OLIMEX/STMP157-BASE-SOM-EVB/HARDWARE/STMP157-BASE-SOM-EVB-Rev.B/3d/SOT-23.step

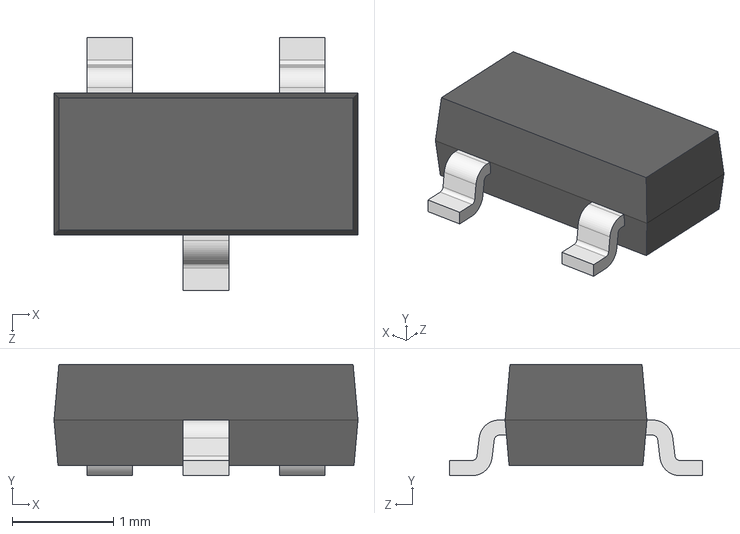
[picture p16: CAD file, 2023-11-24]
HARDWARE/STMP157-BASE-SOM-EVB-Rev.B/3d/SOT-23.step
3.00 x 1.10 x 2.50 mm
