OLIMEX/STMP157-BASE-SOM-EVB/HARDWARE/STMP157-BASE-SOM-EVB-Rev.B/3d/HN1x3-PinHeader_1x03_P2.54mm_Vertical.step

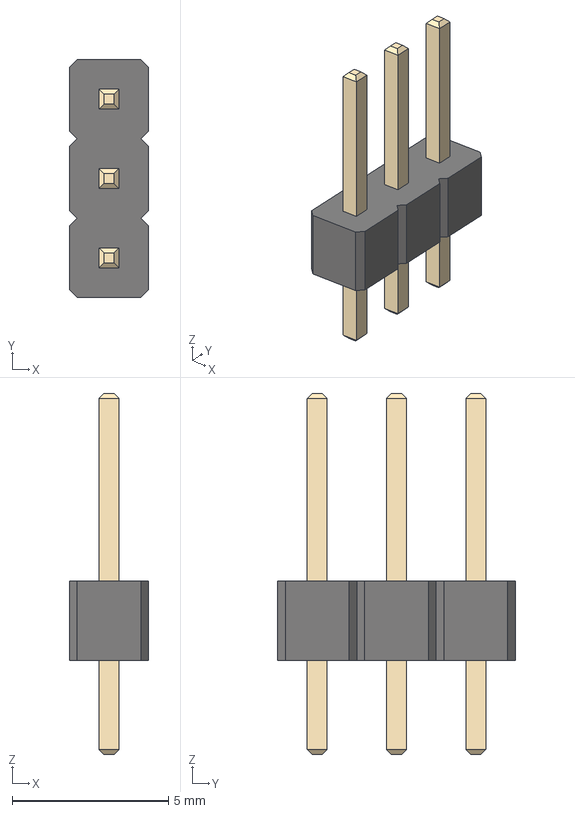
[picture p17: CAD file, 2023-11-24]
HARDWARE/STMP157-BASE-SOM-EVB-Rev.B/3d/HN1x3-PinHeader_1x03_P2.54mm_Vertical.step
2.54 x 7.62 x 11.5 mm
