OLIMEX/STMP157-BASE-SOM-EVB/HARDWARE/STMP157-BASE-SOM-EVB-Rev.B/3d/dshp04ts-s.stp

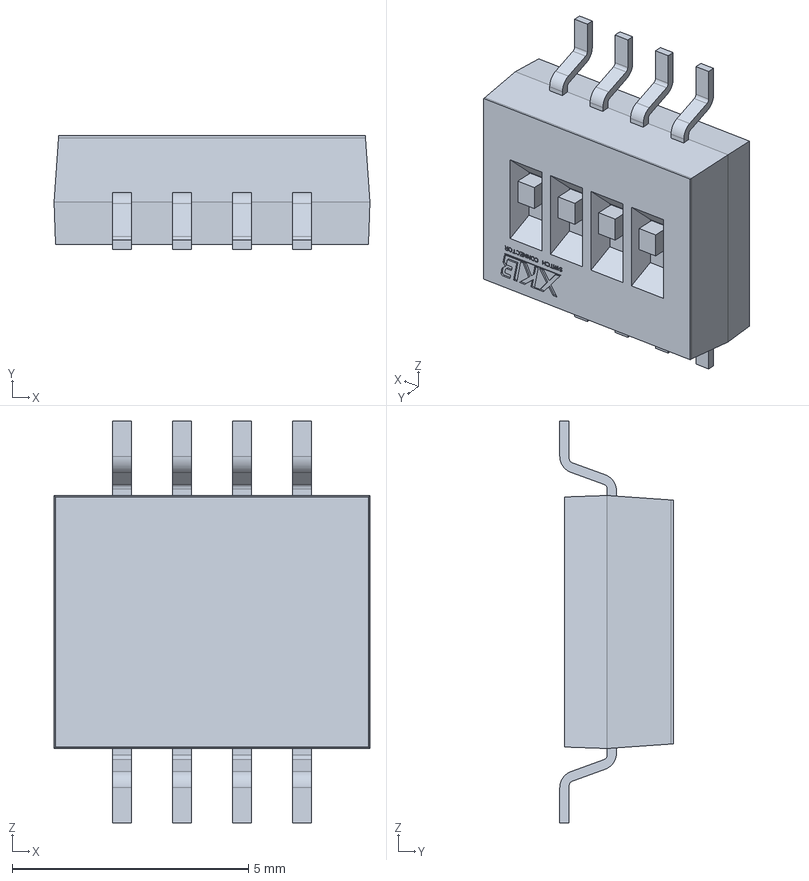
[picture p18: CAD file, 2023-11-24]
HARDWARE/STMP157-BASE-SOM-EVB-Rev.B/3d/dshp04ts-s.stp
6.68 x 2.40 x 8.50 mm
