OLIMEX/STMP157-BASE-SOM-EVB/HARDWARE/STMP157-BASE-SOM-EVB-Rev.B/3d/QFN48-0.5.STEP

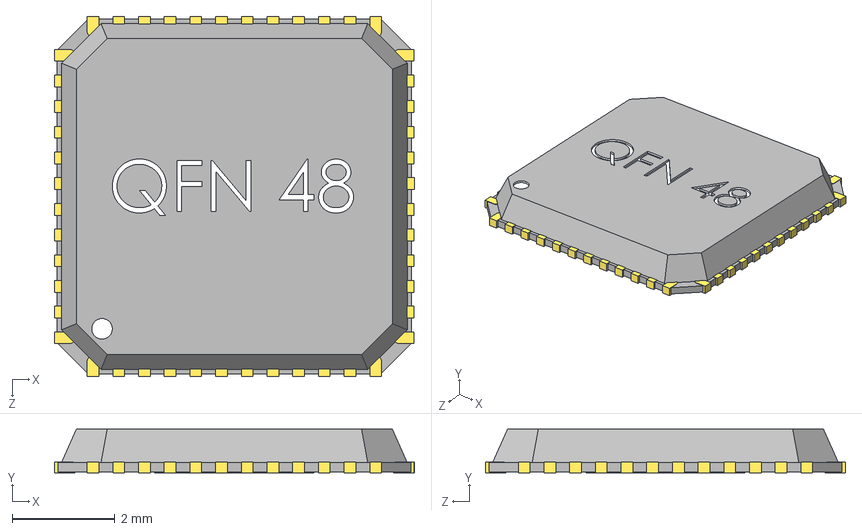
[picture p19: CAD file, 2023-11-24]
HARDWARE/STMP157-BASE-SOM-EVB-Rev.B/3d/QFN48-0.5.STEP
7.00 x 0.85 x 7.01 mm
User Library-QFN48-1_Body
User Library-QFN48-1_Pins
