OLIMEX/STMP157-BASE-SOM-EVB/HARDWARE/STMP157-BASE-SOM-EVB-Rev.B/3d/Audio_Jack-3.5mm---CUI_SJ1-3515-SMT-TR.step

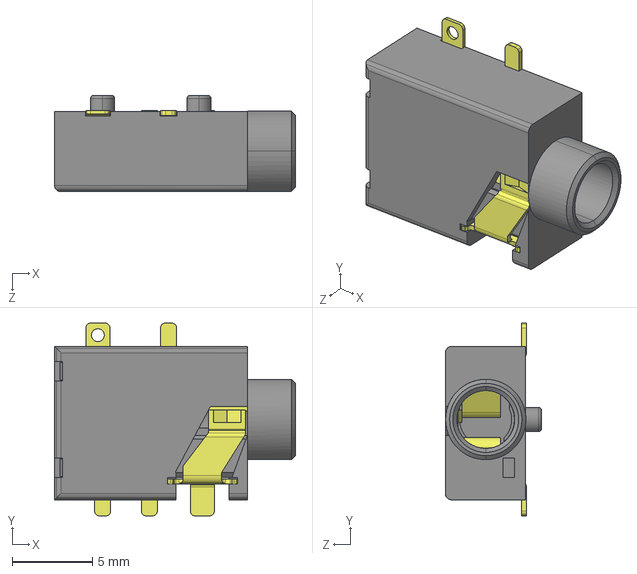
[picture p20: CAD file, 2023-11-24]
HARDWARE/STMP157-BASE-SOM-EVB-Rev.B/3d/Audio_Jack-3.5mm---CUI_SJ1-3515-SMT-TR.step
15.0 x 12.0 x 6.00 mm
