OLIMEX/STMP157-BASE-SOM-EVB/HARDWARE/STMP157-BASE-SOM-EVB-Rev.B/3d/GBH254SMT-40(B-V-40-LF).stp

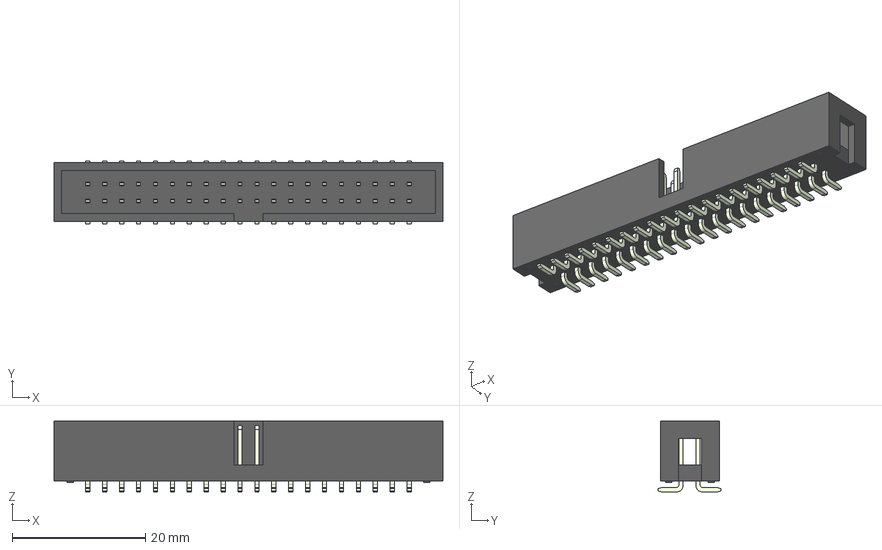
[picture p22: CAD file, 2023-11-24]
HARDWARE/STMP157-BASE-SOM-EVB-Rev.B/3d/GBH254SMT-40(B-V-40-LF).stp
58.4 x 9.50 x 10.6 mm
