OLIMEX/STMP157-BASE-SOM-EVB/HARDWARE/STMP157-BASE-SOM-EVB-Rev.B/3d/JST_B2B-PH-SM4-TB(DW02R).step

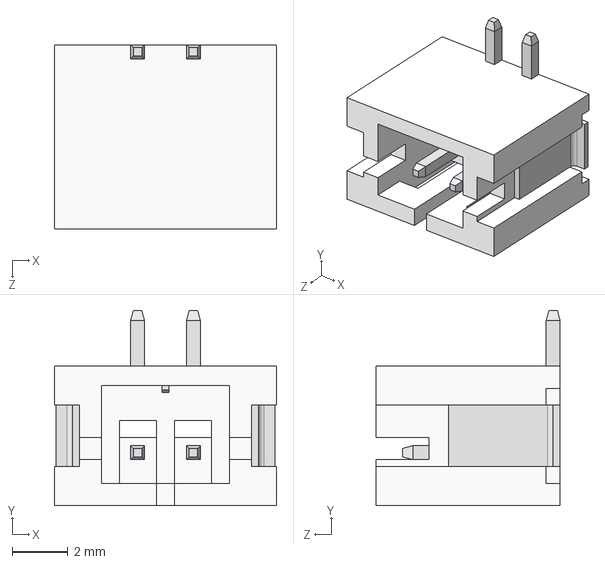
[picture p23: CAD file, 2023-11-24]
HARDWARE/STMP157-BASE-SOM-EVB-Rev.B/3d/JST_B2B-PH-SM4-TB(DW02R).step
7.95 x 7.00 x 6.60 mm
