OLIMEX/STMP157-BASE-SOM-EVB/HARDWARE/STMP157-BASE-SOM-EVB-Rev.B/3d/DF12(3.0)-40DS-0.5V.stp

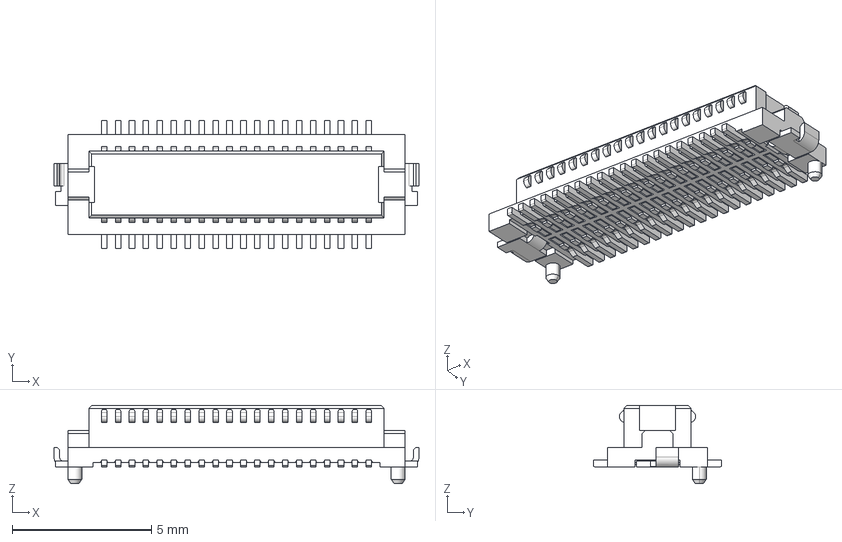
[picture p24: CAD file, 2023-11-24]
HARDWARE/STMP157-BASE-SOM-EVB-Rev.B/3d/DF12(3.0)-40DS-0.5V.stp
13.1 x 4.60 x 2.80 mm
