OLIMEX/STMP157-BASE-SOM-EVB/HARDWARE/STMP157-BASE-SOM-EVB-Rev.B/3d/SOT-223-2.STEP

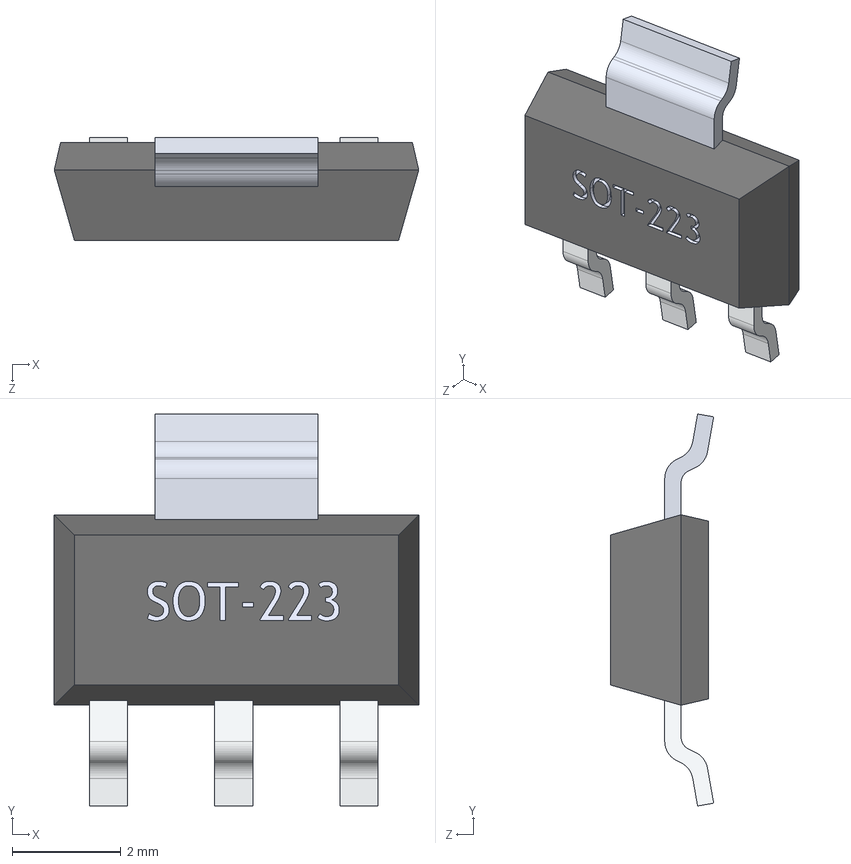
[picture p25: CAD file, 2023-11-24]
HARDWARE/STMP157-BASE-SOM-EVB-Rev.B/3d/SOT-223-2.STEP
6.70 x 7.20 x 1.90 mm
User Library-SOT-223-2_PIN_SOT-223_2_1 x 3
User Library-SOT-223-2_SOT-223_1
User Library-SOT-223-2_PIN_SOT-223_1
