OLIMEX/STMP157-BASE-SOM-EVB/HARDWARE/STMP157-BASE-SOM-EVB-Rev.B/3d/FPV-WZB21-24-LF_Molex-524372433.stp

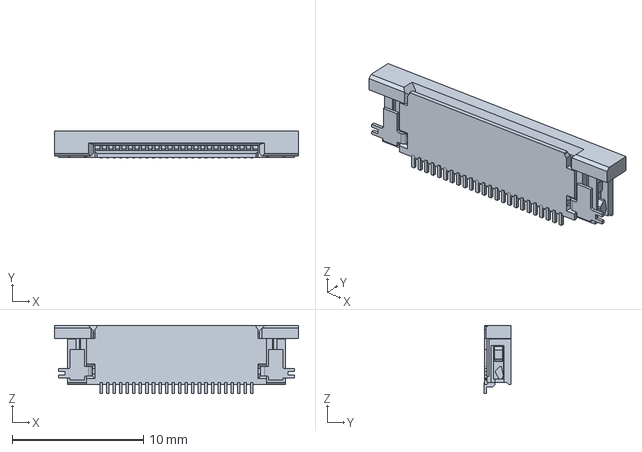
[picture p26: CAD file, 2023-11-24]
HARDWARE/STMP157-BASE-SOM-EVB-Rev.B/3d/FPV-WZB21-24-LF_Molex-524372433.stp
18.6 x 2.04 x 5.20 mm
