OLIMEX/STMP157-BASE-SOM-EVB/HARDWARE/STMP157-BASE-SOM-EVB-Rev.B/3d/TFC-WPAPR-08---112J-TXAR-R_C_1-1.STEP

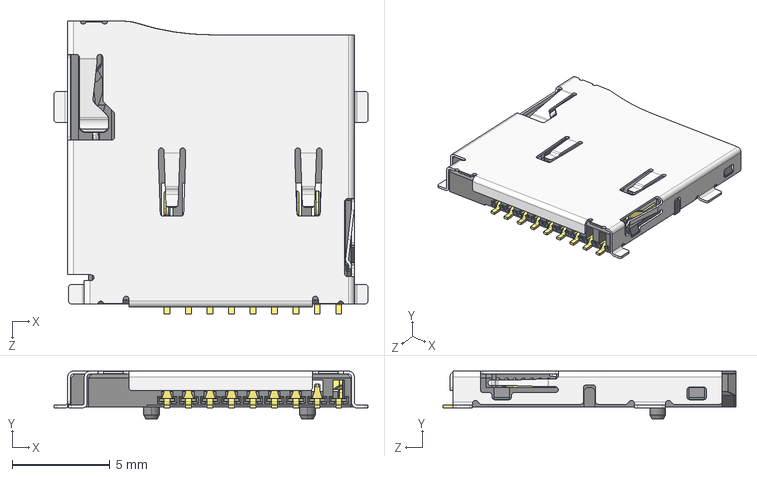
[picture p27: CAD file, 2023-11-24]
HARDWARE/STMP157-BASE-SOM-EVB-Rev.B/3d/TFC-WPAPR-08---112J-TXAR-R_C_1-1.STEP
16.1 x 2.45 x 15.0 mm
