OLIMEX/STMP157-BASE-SOM-EVB/HARDWARE/STMP157-BASE-SOM-EVB-Rev.B/3d/SO-8_150mil---SN65HVDA1050AQDRQ1.STEP

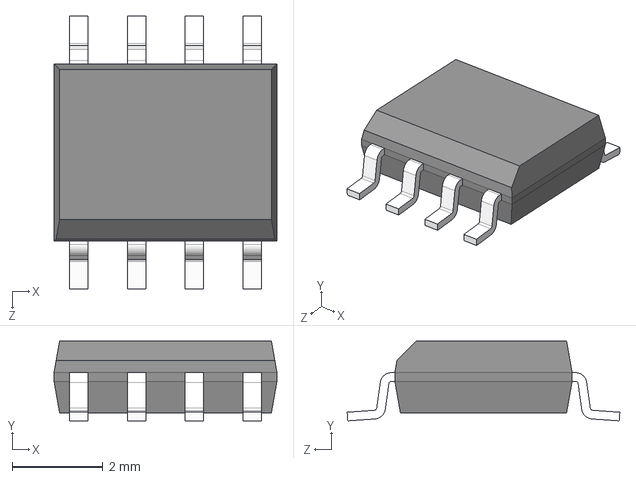
[picture p28: CAD file, 2023-11-24]
HARDWARE/STMP157-BASE-SOM-EVB-Rev.B/3d/SO-8_150mil---SN65HVDA1050AQDRQ1.STEP
4.90 x 1.75 x 5.99 mm
