OLIMEX/STMP157-BASE-SOM-EVB/HARDWARE/STMP157-BASE-SOM-EVB-Rev.B/3d/DO-214AA_SMB.step

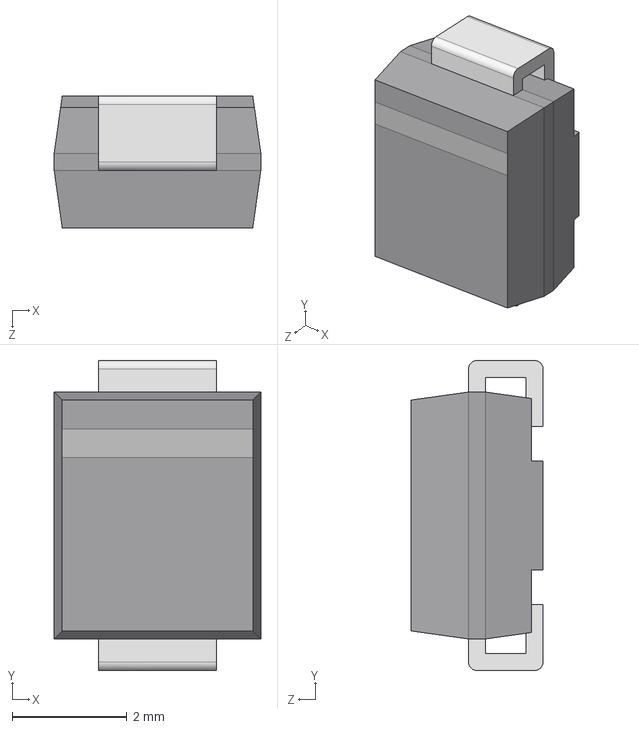
[picture p33: CAD file, 2023-11-24]
HARDWARE/STMP157-BASE-SOM-EVB-Rev.B/3d/DO-214AA_SMB.step
3.60 x 5.40 x 2.30 mm
