OLIMEX/STMP157-BASE-SOM-EVB/HARDWARE/STMP157-BASE-SOM-EVB-Rev.B/3d/GBH254SMT-20(B-V-20-LF)---CH8720xM100.STEP

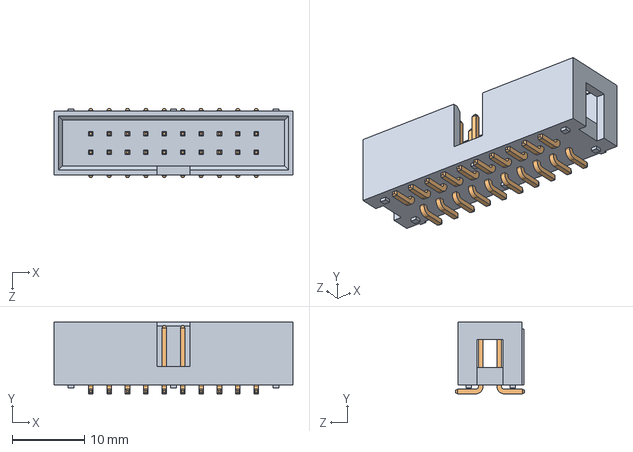
[picture p34: CAD file, 2023-11-24]
HARDWARE/STMP157-BASE-SOM-EVB-Rev.B/3d/GBH254SMT-20(B-V-20-LF)---CH8720xM100.STEP
33.0 x 9.90 x 9.60 mm
CH87 BASE_20
SMT TYPE P x 20
