OLIMEX/STMP157-BASE-SOM-EVB/HARDWARE/STMP157-BASE-SOM-EVB-Rev.B/3d/RaspberryPiLCD-MiPi_Connector-TE_1-1734248-5.stp

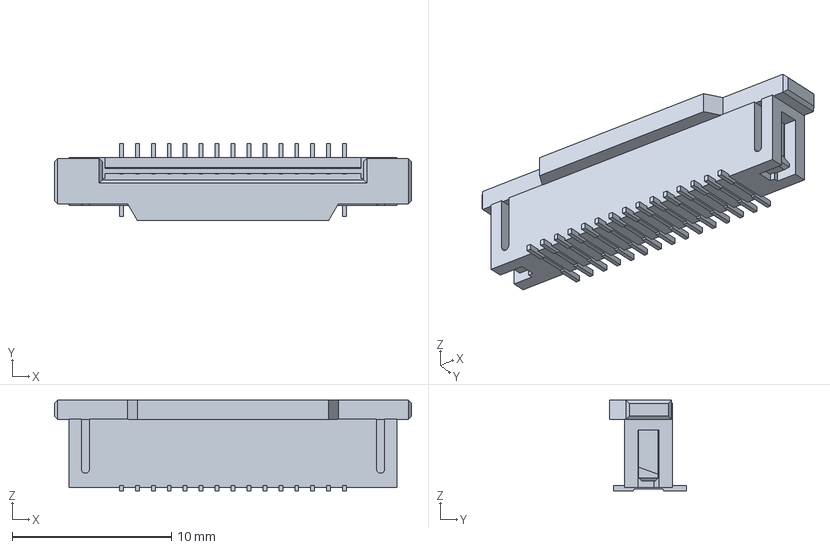
[picture p36: CAD file, 2023-11-24]
HARDWARE/STMP157-BASE-SOM-EVB-Rev.B/3d/RaspberryPiLCD-MiPi_Connector-TE_1-1734248-5.stp
22.4 x 4.85 x 5.68 mm
