OLIMEX/STMP157-BASE-SOM-EVB/HARDWARE/STMP157-BASE-SOM-EVB-Rev.B/STMP15x-BASE-SOM-EVB_Rev_B.sch

## KiCad design HARDWARE/STMP157-BASE-SOM-EVB-Rev.B/STMP15x-BASE-SOM-EVB_Rev_B.sch (2023-11-24)

Schematic: STMP15x-BASE-SOM-EVB_Rev_B.sch

Parts:
1.25_EXT1: TESTPAD; TP_SMD
3.3V/5.0V1, 3.3V/5.0V2: Opened(2-3)/Closed(1-2); SJ_2_SMALL_12_TIED
5V_E1: Opened; SJ_1_SMALLER
ARM-JTAG1: NA(HAB-VCR-010-LF); HAB-VCR-010-LF
BACKUP1: NA(HN1X2); HN1x2
BOOT_SW1: DSHP04TS-S; DSHP04TS-S-1.27mm_Half_4_Slide
C1, C5, C9, C13, C16, C46, C49, C52, C58, C60: 22uF/6.3V/20%/X5R/C0603; C_0603_5MIL_DWS
C2, C3, C4, C30, C31, C35, C50, C55, C65, C66, C67, C68, C69, C70, C86: 47uF/6.3V/20%/X5R/C0805; C_0805_5MIL_DWS
C6: NA(10uF/6.3V/20%/X5R/C0603); C_0603_5MIL_DWS
C7, C8, C26, C27, C34, C36, C37: 10uF/6.3V/20%/X5R/C0603; C_0603_5MIL_DWS
C10, C11, C12, C14, C15, C17, C18, C19, C20, C21, C22, C23, C25, C28, C29, C33, C38, C39, C40, C41, C44, C45, C51, C53, C54, C56, C57, C59, C61, C62, C63, C77, C78, C79, C83, C84: 100nF/10V/10%/X5R/C0402; C_0402_5MIL_DWS
C24, C32: NA(100nF/10V/10%/X5R/C0402); C_0402_5MIL_DWS
C42: NA(15pF/C0402); C_0402_5MIL_DWS
C43: 3.3nF/50V/10%/X5R/C0402; C_0402_5MIL_DWS
C47, C48: 33pF/50V/5%/COG/C0402; C_0402_5MIL_DWS
C64: 1uF/10V/10%/X5R/C0603; C_0603_5MIL_DWS
C71, C72, C73, C74, C75, C76: NA(47uF/6.3V/20%/X5R/C0805); C_0805_5MIL_DWS
C80, C81, C82: NA(24pF/50V/5%/COG/C0402); C_0402_5MIL_DWS
C85: 1nF/2kV/10%/X7R/C1206; C_1206_5MIL_DWS_ISO
C87, C88, C89, C90: NA(560pF/50V/5%/NP0/C0603); C_0603_5MIL_DWS
CAM1: CAMERA-OV2640-120(FPV-WZB21-24-LF); OV2640(FPV-WZB21-24-LF)
CAN1, CAN2: TB3-3.5ММ(HD-351_3P); TB3-3.5mm
CAN_T1, CAN_T2: Opened; SJ_1_SMALLER
D1: 1N5822/SS34/SMA; SMA-KA
D2: SMBJ6.0A; DO214AA_1(K)-2(A)
D3: 1N4007/SMA; SMA-KA
D4: 1N5819S4(SOD123); SOD-123_1C-2A_KA
DBG1: HN1x3
EXT1: P-B-V-40-LF; GBH-254-SMT-40
EXT2: B-V-20-LF(GBH254SMT-20); GBH-254-SMT-20
FET1, FET3: IRLML6402(SOT-23); SOT23
FET2: BSS138(SOT-23); SOT23
FID1, FID2, FID3, FID4, FID5, FID6: Fiducial; Fiducial1x3
FUSE1: NA(5025); FUSE-5025
FUSE2: FSMD035; FUSE-1206
Flash_Con1: DF12(3.0)-40DS-0.5V(51); Flash_Con[DF12(3.0)-40DS-0.5V(86)]
GPIO1, GPIO2, GPIO3, GPIO4, GPIO5, GPIO6: MALE-PAV16X-2x20-HIGH; GPH127SMT-02X20(PA-V16X-2X20-LF)
HDMI1: HDMI-SWM-19
HEADPHONES1: PJ-3.5-365-3P(SCJ325P00XG0B02G); SCJ325P00XG0B02G
L1: 2.2uH/3A/YS75/7x8; YS75_7X8MM
L2, L3, L4, L5, L6, L7, L8, L9, L12: FB0805/600R/2A; L_0805_5MIL_DWS
L10, L11: NA(2.7nH/L0402); L_0402_5MIL_DWS
LAN1: TM211Q01FM22
LiPo_BAT1: DW02R; LIPO_BAT-CON2DW02R
MH1, MH2, MH3, MH4, MH5, MH6, MH7, MH8: Mounting_Hole_NPTH; Mounting_Hole_Drill-3.3mm_Clerance-7mm
MICROPHONE1: PJ-3.5-365-3P(SCJ325P00XG0B02G); SCJ325P00XG0B02G
MICRO_SD1: TFC-WPAPR-08-LF; TFC-WPAPR-08
MiPi-LCD1: FPA-VZA2-15-LF; TE_1-1734248-5
PWR1: PWRJ-2mm(YDJ-1134)
PWR2: YTS-A016-X
PWRLED1: LED/Red/0603; LED_0603_KA
Q1: Q25MHz/20pF/20ppm/4P/3.2x2.5mm; TSX-3.2x2.5mm_GND(3)
R1, R6, R14, R16, R21, R25, R28, R29, R32, R33, R36, R39, R52, R57, R58, R59, R60, R62, R73, R77, R82, R85: 10k/R0402; R_0402_5MIL_DWS
R2: 1M/R0402; R_0402_5MIL_DWS
R3, R7, R9, R10, R11, R26, R27, R31, R34, R45, R51: 2.2k/R0402; R_0402_5MIL_DWS
R4: 8.25k/1%/R0402; R_0402_5MIL_DWS
R5: 1.1k/1%/R0402; R_0402_5MIL_DWS
R8, R46, R47: 330R/R0402; R_0402_5MIL_DWS
R12, R17, R18, R19, R22, R24, R41, R42, R67, R75, R76, R78, R79, R81: 22R/R0402; R_0402_5MIL_DWS
R13, R15, R35, R38, R43, R44, R56, R61, R66, R84: NA/R0402; R_0402_5MIL_DWS
R20: 5.6k/R0402; R_0402_5MIL_DWS
R23: NA(22R/R0402); R_0402_5MIL_DWS
R30: 10R/R0402; R_0402_5MIL_DWS
R37, R40, R50: 120R/R1206; R_1206_5MIL_DWS
R48, R49: 680R/R0402; R_0402_5MIL_DWS
R53: 12.1k/1%/R0603; R_0603_5MIL_DWS
R54, R83: 100k/R0402; R_0402_5MIL_DWS
R55, R68, R69, R70, R71, R72, R74, R80: 1k/R0402; R_0402_5MIL_DWS
R63: 13k/1%/R0402; R_0402_5MIL_DWS
R64, R65: 6.81k/1%/R0402; R_0402_5MIL_DWS
R86, R89, R90: 0R/R0402; R_0402_5MIL_DWS
R87, R88: NA(0R/R0402); R_0402_5MIL_DWS
R91, R92: NA(2.2k/R0402); R_0402_5MIL_DWS
RGB-LCD1: P-B-V-40-LF; GBH-254-SMT-40
RM1, RM3, RM4: RA0805_(4X0402)_22R; RA0805_(4X0402)_xx_BIGGEROUTPADS
RM2: RA0805_(4X0402)_4.7k; RA0805_(4X0402)_xx_BIGGEROUTPADS
RM5: RA1206_(4x0603)_4B8_100k; RA1206_(4X0603)_4B8_xx
RST1: YTS-A016-X
TVS1, TVS2: ESDS314DBVR(SOT-23-5); SOT-23-5
U1: NA(MCP121T475I-TT(SOT23-3)); SOT-23
U2: MT3608(SOT23-6); SOT23-6
U3, U4, U5: NA(RCLAMP0524P(SLP2510P8)); SLP2510P8_TEST
U6: IT66121FN(QFN-64); QFN64_9x9mm_Pitch_0.5mm_65PAD_4.5mm
U7: ES8388(QFN28); QFN28_EP(29)_4.076x4.076x0.9mm_Pitch_0.45mm
U8, U9: SIT1050T(SOIC-8_150mil); SOIC-8_150mil
U10, U11, U12: SY6280AAC(SOT23-5); SOT-23-5
U13: KSZ9031RNXCC-TR(QFN48_1DRILL(PADPITCH-0.5MM)); QFN48_1DRILL(PADPITCH-0.5MM)
U14: VDA4510CTA(SOT23-3); SOT-23
UEXT1: P-B-V-10-LF; GBH-254-SMT-10
USB1, USB2: USB_A_VERTICAL; USB_A_VERTICAL_PTH
USB-OTG1: USB-OTG(MSB-SW-5AB-LF); USB_MINI_9PIN
VR1: LD1117AG-AD-AA3-A-R; SOT223

Notes on the sheet:
LI-ION_BATTERY 4.2V
EVB to SOM - Interconnecting connectors
Fiducials
RGB-LCD
I2C Address: 0x50-0x57
Gigabit Ethernet
RLC filter close to the MCU!
RLC filter close to the PHY!
RC filter close to the PHY!
Mounting Holes
Vout=0.6*(1+Ra/Rb)
+5VDC ONLY!!!
USB
Ilim(A)=6800/Rset(Ohm)
Rset
Ilim=1A
Ilim=0.5A
CAN1&2
UEXT
Power Supply
Compared with STMP157-OLinuXino-LIME2, STMP15x-BASE-SOM-EVB has got the following additional modules: + CAN2, UEXT, Audio, JTAG, MiPi-LCD(DSI), CSI-Camera, Extensions
Boot Selection
eMMC/NAND/SPI-Flash
HDMI
I2C Address: 0x4D
Audio Codec
I2C Address: 0x20, when AD0 is pulled down I2C Address: 0x22, when AD0 is pulled up
Audio In
Audio Out
JTAG_RTCK
Debug JTAG
Buttons
Debug UART
I2C Address (Slave Address): ???
MiPi-LCD
The MiPi-LCD connector is RPi Compatible!
T-Card
CSI-CAMERA
I2C Address: 0x30
Extensions
Option!
====================== STRAP-IN OPTIONS - KSZ9031RNX ====================== The PHY address, PHYAD[2:0]=001 The MODE[3:0] = 1111 RGMII mode - Advertise all capabilities (10/100/1000 speed half-/full-duplex) CLK125_EN Pull-up (1) = Enable 125 MHz clock output LED_MODE Pull-up (1) = Single-LED mode
2.0 MegaPixel
Boot Mode
BOOT2
BOOT1
BOOT0
Reserved (NoBoot)
NOR -> Serial NOR Flash on QUADSPI
NAND -> Serial NAND Flash on QUADSPI
eMMC on SDMMC2
SD-Card on SDMMC1 (default)
Forced UART/USB Boot. USB high-speed device, or USART2/3/6 and UART4/5/7/8 on default pins.
NAND -> SLC NAND Flash on FMC
OFF
Option to switch over between I2C1 and I2C6.
